SandorBalazsHU/electronic-experiments-01-square-triangle-sine-wave/oscilloscope-images/5vpp-composite/6.bmp

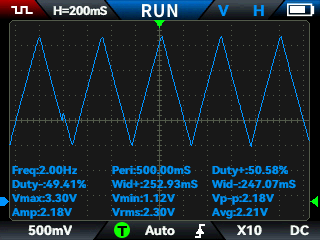
oscilloscope-images/5vpp-composite/6.bmp
