SandorBalazsHU/electronic-experiments-01-square-triangle-sine-wave/oscilloscope-images/5vpp/1.bmp

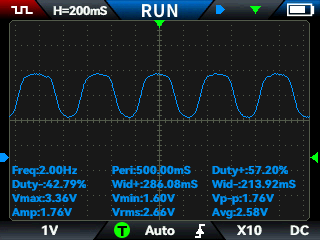
oscilloscope-images/5vpp/1.bmp
