SandorBalazsHU/electronic-experiments-01-square-triangle-sine-wave/oscilloscope-images/5vpp/7.bmp

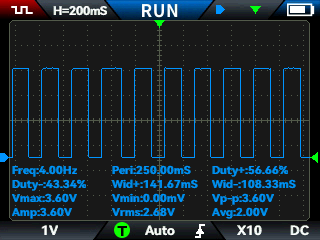
oscilloscope-images/5vpp/7.bmp
