SandorBalazsHU/electronic-experiments-01-square-triangle-sine-wave/oscilloscope-images/12vpp/28.bmp

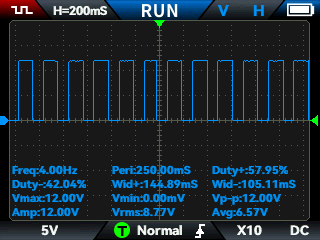
oscilloscope-images/12vpp/28.bmp
